ahein624/KnockBlock/auth.py

"""Password + API-token auth backed by auth.json next to the app.

The password is set from the shell (`python3 app.py --set-password`), never
through the web — an internet-exposed sign with no password yet shouldn't be
claimable by whoever visits first. The API token authenticates scripted
clients (Stream Deck, curl) without a browser session.
"""
import hmac
import json
import secrets
import threading
from pathlib import Path

from werkzeug.security import check_password_hash, generate_password_hash

AUTH_FILE = Path(__file__).resolve().parent / "auth.json"

_lock = threading.Lock()
_data = None
_loaded_mtime = None


def _load():
    """Read auth.json, re-reading if it changed on disk — `--set-password`
    runs in a separate process while the server keeps running."""
    global _data, _loaded_mtime
    try:
        mtime = AUTH_FILE.stat().st_mtime
    except FileNotFoundError:
        mtime = None
    if _data is None or mtime != _loaded_mtime:
        try:
            _data = json.loads(AUTH_FILE.read_text())
        except (FileNotFoundError, ValueError):
            _data = {}
        _loaded_mtime = mtime
    return _data


def _save():
    global _loaded_mtime
    tmp = AUTH_FILE.with_suffix(".auth.tmp")
    tmp.write_text(json.dumps(_data))
    tmp.chmod(0o600)
    tmp.replace(AUTH_FILE)
    _loaded_mtime = AUTH_FILE.stat().st_mtime


def secret_key():
    """Stable Flask session key, so logins survive server restarts."""
    with _lock:
        data = _load()
        if not data.get("secret_key"):
            data["secret_key"] = secrets.token_hex(32)
            _save()
        return data["secret_key"]


def password_set():
    return bool(_load().get("password_hash"))


def check_password(password):
    stored = _load().get("password_hash")
    return bool(stored) and check_password_hash(stored, password)


def set_password(password):
    with _lock:
        data = _load()
        # pbkdf2 rather than werkzeug's scrypt default: scrypt needs
        # OpenSSL 1.1+ in hashlib, which not every Python build has.
        data["password_hash"] = generate_password_hash(password, method="pbkdf2:sha256")
        if not data.get("api_token"):
            data["api_token"] = secrets.token_urlsafe(24)
        _save()


def api_token():
    with _lock:
        data = _load()
        if not data.get("api_token"):
            data["api_token"] = secrets.token_urlsafe(24)
            _save()
        return data["api_token"]


def check_token(token):
    stored = _load().get("api_token")
    return bool(stored) and hmac.compare_digest(stored, token)


def regenerate_token():
    with _lock:
        data = _load()
        data["api_token"] = secrets.token_urlsafe(24)
        _save()
        return data["api_token"]


def untrusted_proxies():
    """LAN addresses that relay outside traffic (e.g. a reverse proxy).

    Requests from these never count as local even though the address is
    private. Site-specific, so configured by hand in auth.json.
    """
    values = _load().get("untrusted_proxies")
    return [str(v) for v in values] if isinstance(values, list) else []


def public_host():
    """Hostname the sign is published under; requests for it always
    require auth. Configured by hand in auth.json."""
    host = _load().get("public_host")
    return str(host).lower() if host else None


def giphy_key():
    """Personal Giphy API key (auth.json "giphy_key"). None means media.py
    falls back to the public demo keys."""
    key = _load().get("giphy_key")
    return str(key) if key else None
